SietseAchterop/Batradio/batradio_pcb/testopamp.asc

C1: cap; 1µ
C2: cap; 0.1µ
R1: res; 20k
R2: res; 1k
R3: res; 8.6k
R4: res; 10k
U1: LMH6629
V1: voltage; ""; AC 0.01
V2: voltage; 3.3
Named nets: 0, V3.3
.ac dec 100 100 10meg
