SietseAchterop/Batradio/batradio_pcb/lt_radio.asc

C1: cap; 1µ
C2: cap; 1µ
C3: cap; 1µ
C4: cap; 1µ
C5: cap; 1µ
C6: cap; 0.1µ
C8: cap; 0.1µ
R1: res; 1k
R2: res; 1k
R3: res; 10k
R4: res; 10k
R5: res; 1k
R6: res; 1k
R7: res; 10k
R8: res; 560
R9: res; 12k
R10: res; 560
R11: res; 50
R12: res; 10k
R13: res; 10k
R14: res; 10k
R15: res; 10k
R16: res; 100
R17: res; 900
U1: LTC6403-1
U2: LT6231
U3: LT6231
V2: voltage; 3.3
V3: voltage; ""; AC 0.001
Named nets: 0, V3.3, v3.3
3volt voeding fg-23629-p16
3.3 volt voeding via diode
.ac dec 100 100 10meg
hier het low pass filter
bypass via jumper of R7  aanpassen
1KOhm lin potentiometer
